pashamray/SG-420M/firmware/src/sin256.asm

       .DB 0x00,0x00,0xC9,0x00,0x92,0x01,0x5B,0x02
       .DB 0x24,0x03,0xED,0x03,0xB6,0x04,0x7F,0x05
       .DB 0x48,0x06,0x11,0x07,0xD9,0x07,0xA2,0x08
       .DB 0x6A,0x09,0x33,0x0A,0xFB,0x0A,0xC4,0x0B
       .DB 0x8C,0x0C,0x54,0x0D,0x1C,0x0E,0xE3,0x0E
       .DB 0xAB,0x0F,0x72,0x10,0x3A,0x11,0x01,0x12
       .DB 0xC8,0x12,0x8F,0x13,0x55,0x14,0x1C,0x15
       .DB 0xE2,0x15,0xA8,0x16,0x6E,0x17,0x33,0x18
       .DB 0xF9,0x18,0xBE,0x19,0x82,0x1A,0x47,0x1B
       .DB 0x0B,0x1C,0xCF,0x1C,0x93,0x1D,0x57,0x1E
       .DB 0x1A,0x1F,0xDD,0x1F,0x9F,0x20,0x61,0x21
       .DB 0x23,0x22,0xE5,0x22,0xA6,0x23,0x67,0x24
       .DB 0x28,0x25,0xE8,0x25,0xA8,0x26,0x67,0x27
       .DB 0x26,0x28,0xE5,0x28,0xA3,0x29,0x61,0x2A
       .DB 0x1F,0x2B,0xDC,0x2B,0x99,0x2C,0x55,0x2D
       .DB 0x11,0x2E,0xCC,0x2E,0x87,0x2F,0x41,0x30
       .DB 0xFB,0x30,0xB5,0x31,0x6E,0x32,0x26,0x33
       .DB 0xDF,0x33,0x96,0x34,0x4D,0x35,0x04,0x36
       .DB 0xBA,0x36,0x6F,0x37,0x24,0x38,0xD9,0x38
       .DB 0x8C,0x39,0x40,0x3A,0xF2,0x3A,0xA5,0x3B
       .DB 0x56,0x3C,0x07,0x3D,0xB8,0x3D,0x68,0x3E
       .DB 0x17,0x3F,0xC5,0x3F,0x73,0x40,0x21,0x41
       .DB 0xCE,0x41,0x7A,0x42,0x25,0x43,0xD0,0x43
       .DB 0x7A,0x44,0x24,0x45,0xCD,0x45,0x75,0x46
       .DB 0x1C,0x47,0xC3,0x47,0x69,0x48,0x0F,0x49
       .DB 0xB4,0x49,0x58,0x4A,0xFB,0x4A,0x9D,0x4B
       .DB 0x3F,0x4C,0xE0,0x4C,0x81,0x4D,0x20,0x4E
       .DB 0xBF,0x4E,0x5D,0x4F,0xFB,0x4F,0x97,0x50
       .DB 0x33,0x51,0xCE,0x51,0x68,0x52,0x02,0x53
       .DB 0x9B,0x53,0x32,0x54,0xC9,0x54,0x60,0x55
       .DB 0xF5,0x55,0x8A,0x56,0x1D,0x57,0xB0,0x57
       .DB 0x42,0x58,0xD3,0x58,0x64,0x59,0xF3,0x59
       .DB 0x82,0x5A,0x0F,0x5B,0x9C,0x5B,0x28,0x5C
       .DB 0xB3,0x5C,0x3E,0x5D,0xC7,0x5D,0x4F,0x5E
       .DB 0xD7,0x5E,0x5D,0x5F,0xE3,0x5F,0x68,0x60
       .DB 0xEB,0x60,0x6E,0x61,0xF0,0x61,0x71,0x62
       .DB 0xF1,0x62,0x70,0x63,0xEE,0x63,0x6C,0x64
       .DB 0xE8,0x64,0x63,0x65,0xDD,0x65,0x56,0x66
       .DB 0xCF,0x66,0x46,0x67,0xBC,0x67,0x32,0x68
       .DB 0xA6,0x68,0x19,0x69,0x8B,0x69,0xFD,0x69
       .DB 0x6D,0x6A,0xDC,0x6A,0x4A,0x6B,0xB7,0x6B
       .DB 0x23,0x6C,0x8E,0x6C,0xF8,0x6C,0x61,0x6D
       .DB 0xC9,0x6D,0x30,0x6E,0x96,0x6E,0xFB,0x6E
       .DB 0x5E,0x6F,0xC1,0x6F,0x22,0x70,0x83,0x70
       .DB 0xE2,0x70,0x40,0x71,0x9D,0x71,0xF9,0x71
       .DB 0x54,0x72,0xAE,0x72,0x07,0x73,0x5E,0x73
       .DB 0xB5,0x73,0x0A,0x74,0x5F,0x74,0xB2,0x74
       .DB 0x04,0x75,0x55,0x75,0xA5,0x75,0xF3,0x75
       .DB 0x41,0x76,0x8D,0x76,0xD8,0x76,0x22,0x77
       .DB 0x6B,0x77,0xB3,0x77,0xFA,0x77,0x3F,0x78
       .DB 0x84,0x78,0xC7,0x78,0x09,0x79,0x4A,0x79
       .DB 0x89,0x79,0xC8,0x79,0x05,0x7A,0x41,0x7A
       .DB 0x7C,0x7A,0xB6,0x7A,0xEE,0x7A,0x26,0x7B
       .DB 0x5C,0x7B,0x91,0x7B,0xC5,0x7B,0xF8,0x7B
       .DB 0x29,0x7C,0x59,0x7C,0x88,0x7C,0xB6,0x7C
       .DB 0xE3,0x7C,0x0E,0x7D,0x39,0x7D,0x62,0x7D
       .DB 0x89,0x7D,0xB0,0x7D,0xD5,0x7D,0xFA,0x7D
       .DB 0x1D,0x7E,0x3E,0x7E,0x5F,0x7E,0x7E,0x7E
       .DB 0x9C,0x7E,0xB9,0x7E,0xD5,0x7E,0xEF,0x7E
       .DB 0x09,0x7F,0x21,0x7F,0x37,0x7F,0x4D,0x7F
       .DB 0x61,0x7F,0x74,0x7F,0x86,0x7F,0x97,0x7F
       .DB 0xA6,0x7F,0xB4,0x7F,0xC1,0x7F,0xCD,0x7F
       .DB 0xD8,0x7F,0xE1,0x7F,0xE9,0x7F,0xF0,0x7F
       .DB 0xF5,0x7F,0xF9,0x7F,0xFD,0x7F,0xFE,0x7F
       .DB 0xFF,0x7F
